gizi92/EDU_IoT/mcus/arduino_uno/examples/IR_led_test/IR_led_test.ino

#include <Wire.h>

volatile int switchState = 0;
const int switchPin = 14;
const int relayPin = 9;

void setup() {
  // put your setup code here, to run once:
  pinMode(relayPin,OUTPUT);
  Serial.begin(9600);
}

void loop() {
  // put your main code here, to run repeatedly:
  digitalWrite(relayPin, HIGH);
  delay(1000);
  digitalWrite(relayPin, LOW);
  delay(1000);
}
