gizi92/EDU_IoT/mcus/arduino_uno/examples/DS3231_simple/DS3231_simple.ino

//www.elegoo.com
//2016.06.13

/*
  DS3231: Real-Time Clock. Simple example
  Read more: www.jarzebski.pl/arduino/komponenty/zegar-czasu-rzeczywistego-rtc-ds3231.html
  GIT: https://github.com/jarzebski/Arduino-DS3231
  Web: http://www.jarzebski.pl
  (c) 2014 by Korneliusz Jarzebski
*/

#include <Wire.h>
#include <DS3231.h>

DS3231 clock;
RTCDateTime dt;

void setup()
{
  Serial.begin(115200);

  // Initialize DS3231
  Serial.println("Initialize DS3231");;
  clock.begin();

  // Set sketch compiling time
  // clock.setDateTime(__DATE__, __TIME__);
}

void loop()
{
  dt = clock.getDateTime();

  // For leading zero look to DS3231_dateformat example

  Serial.print("Raw data: ");
  Serial.print(dt.year);   Serial.print("-");
  Serial.print(dt.month);  Serial.print("-");
  Serial.print(dt.day);    Serial.print(" ");
  Serial.print(dt.hour);   Serial.print(":");
  Serial.print(dt.minute); Serial.print(":");
  Serial.print(dt.second); Serial.println("");

  delay(1000);
}
